wfites/TF-AtticFanController/AtticFanControllerBreadBoardExp.jpg

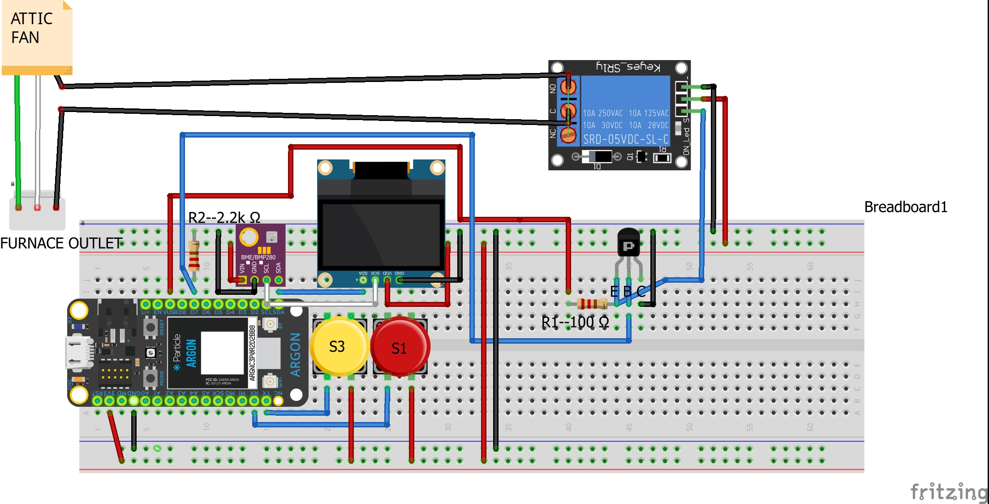
AtticFanControllerBreadBoardExp.jpg
