wfites/TF-AtticFanController/Photos/ControllerAutoModeScreen.jpg

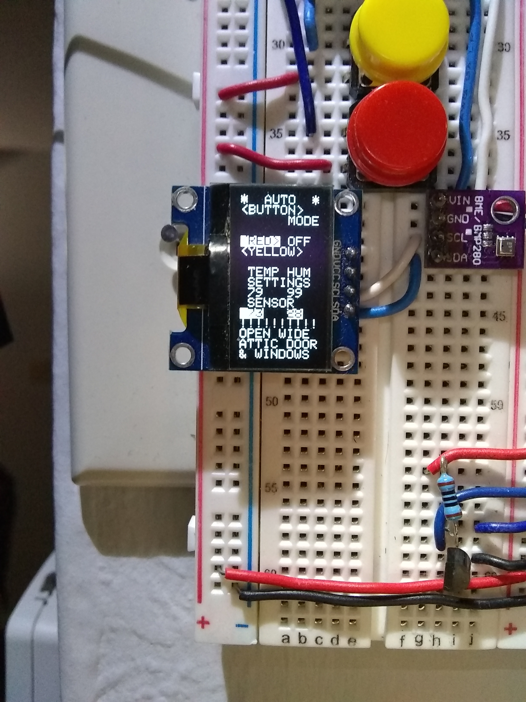
Photos/ControllerAutoModeScreen.jpg
