wfites/TF-AtticFanController/Photos/FanAccessDoorClosed.JPG

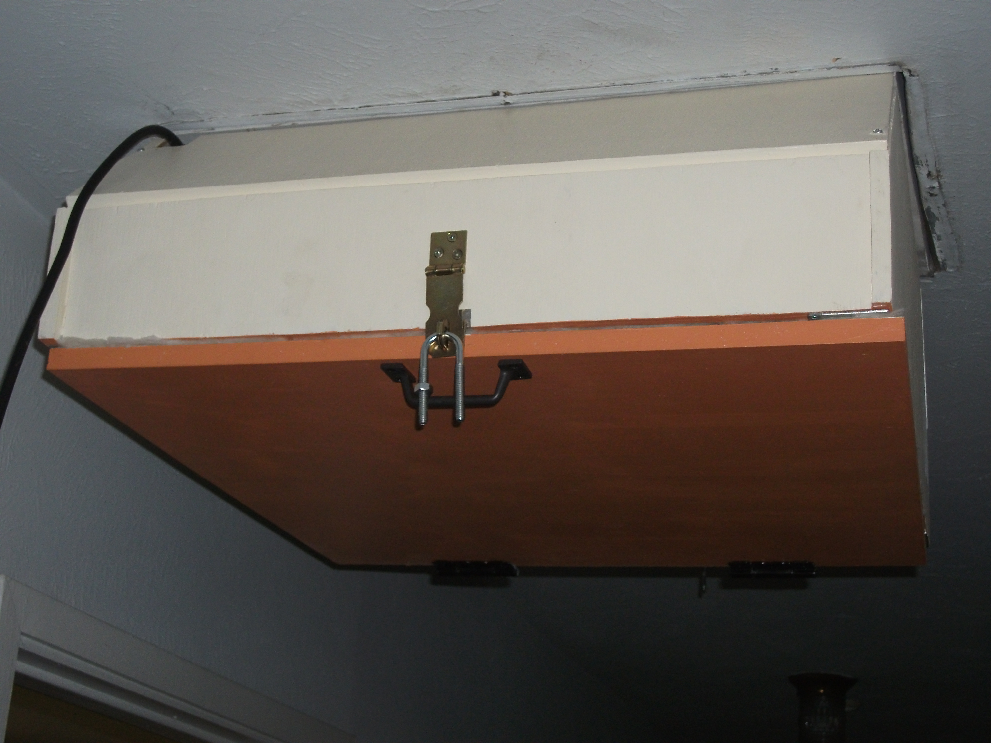
Photos/FanAccessDoorClosed.JPG
