wfites/TF-AtticFanController/Photos/FanAccessDoorOpen.JPG

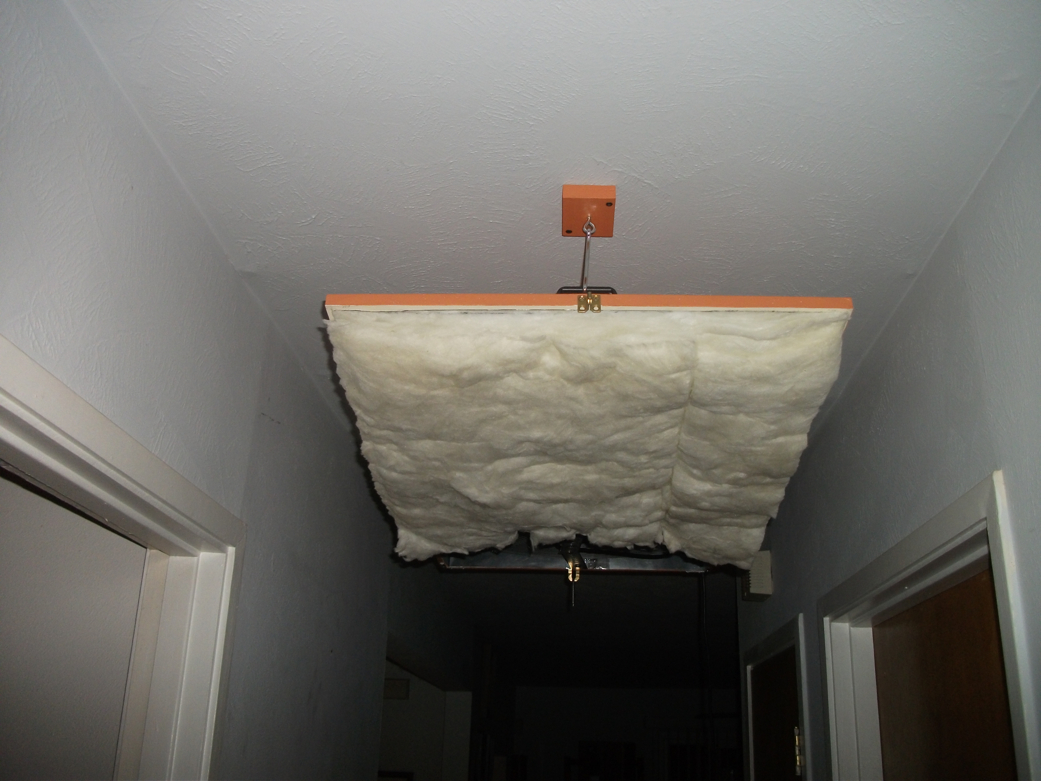
Photos/FanAccessDoorOpen.JPG
