wfites/TF-AtticFanController/Photos/FanCompartmentInterior - Copy.JPG

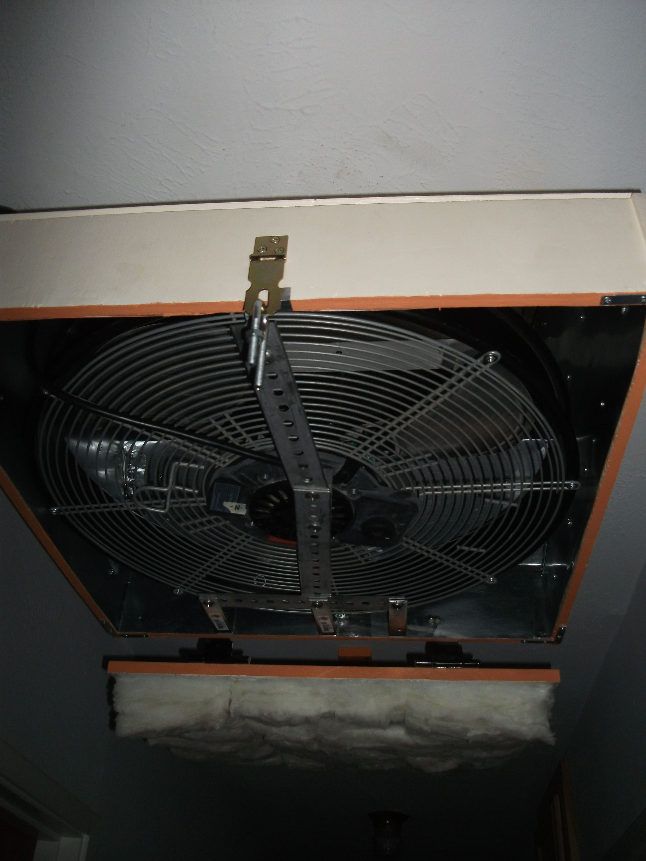
Photos/FanCompartmentInterior - Copy.JPG
