wfites/TF-AtticFanController/Photos/BeadboardCircuitOnWallTestCrop.jpg

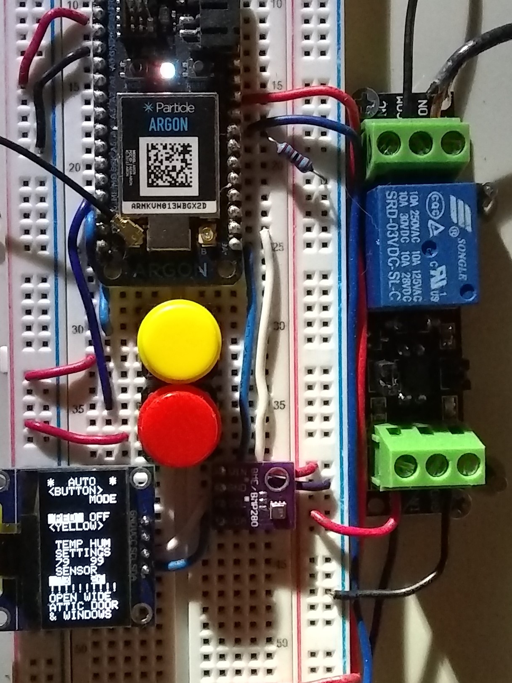
Photos/BeadboardCircuitOnWallTestCrop.jpg
