wfites/TF-AtticFanController/Photos/FanCompartmentAndAccessDoorJ-Hook.JPG

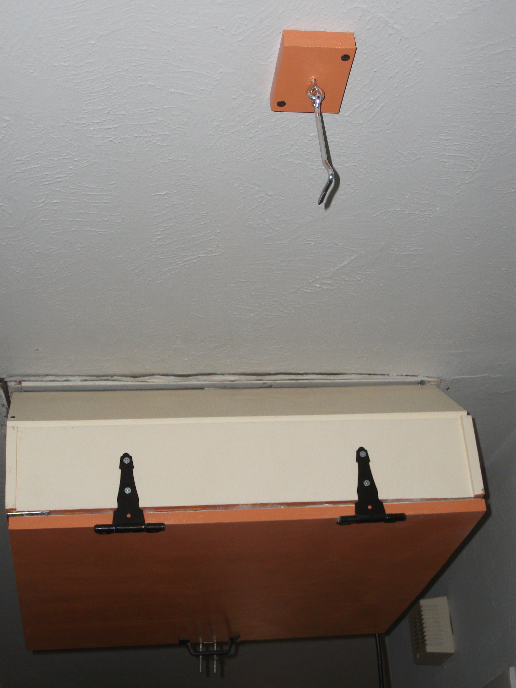
Photos/FanCompartmentAndAccessDoorJ-Hook.JPG
